GCY/GPS-Nixie-Clock/wxNixieClock/in16/0.png

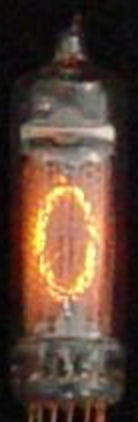
wxNixieClock/in16/0.png
