GCY/GPS-Nixie-Clock/wxNixieClock/in16/1.png

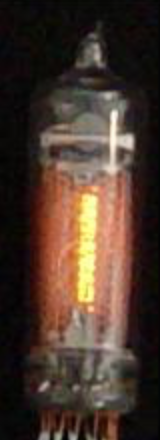
wxNixieClock/in16/1.png
