GCY/GPS-Nixie-Clock/wxNixieClock/in16/2.png

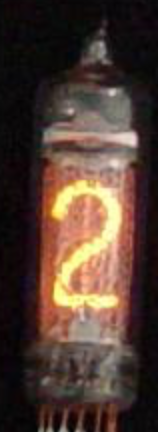
wxNixieClock/in16/2.png
