GCY/GPS-Nixie-Clock/wxNixieClock/in16/3.png

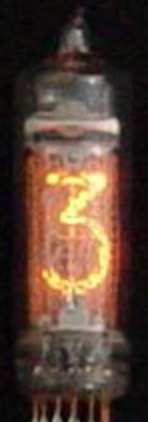
wxNixieClock/in16/3.png
