GCY/GPS-Nixie-Clock/wxNixieClock/in16/5.png

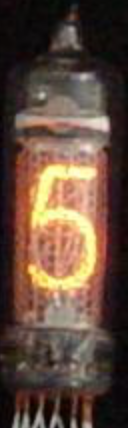
wxNixieClock/in16/5.png
