GCY/GPS-Nixie-Clock/wxNixieClock/in16/6.png

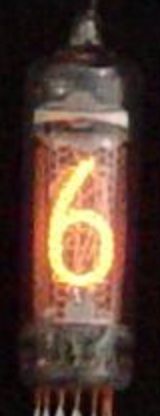
wxNixieClock/in16/6.png
