GCY/GPS-Nixie-Clock/wxNixieClock/in16/7.png

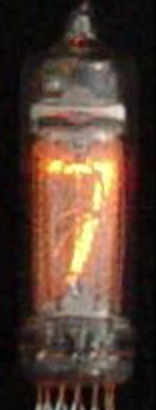
wxNixieClock/in16/7.png
