GCY/GPS-Nixie-Clock/wxNixieClock/in16/8.png

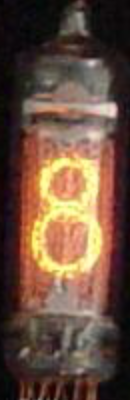
wxNixieClock/in16/8.png
