GCY/GPS-Nixie-Clock/wxNixieClock/in16/9.png

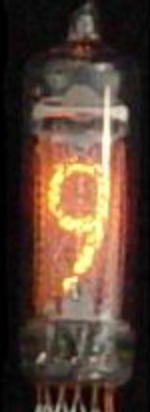
wxNixieClock/in16/9.png
